Moragor/SC_Mining_Controller/Pictures/1.JPG

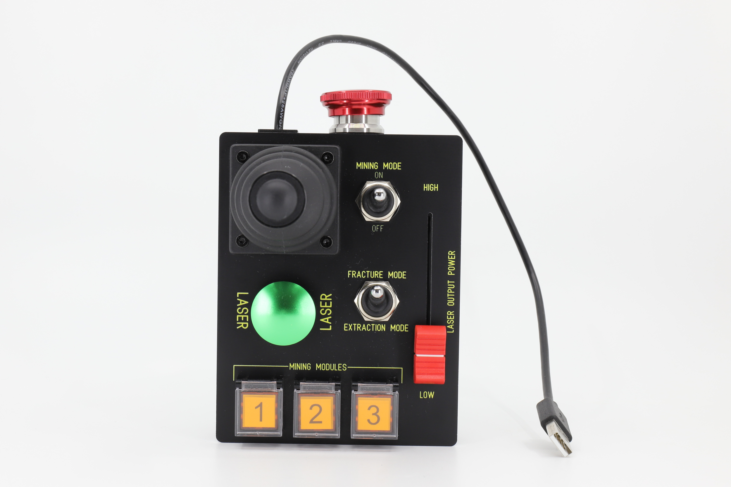
Pictures/1.JPG
