Moragor/SC_Mining_Controller/Pictures/2.JPG

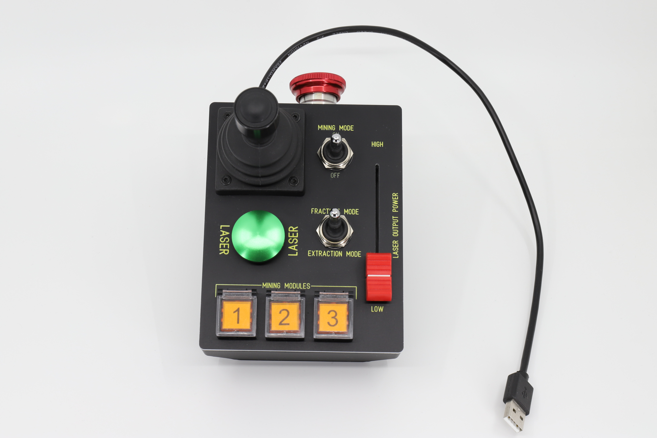
Pictures/2.JPG
