Moragor/SC_Mining_Controller/Pictures/3.JPG

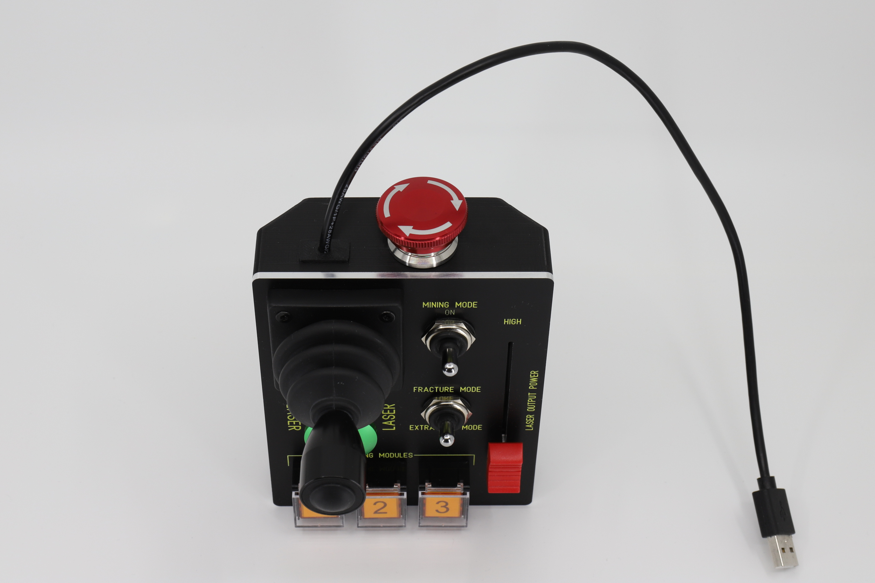
Pictures/3.JPG
